teixeluis/clustered-heating-controller/docs/adapter_board/io_adapter_board.kicad_sch

## KiCad design docs/adapter_board/io_adapter_board.kicad_sch (2024-08-31)

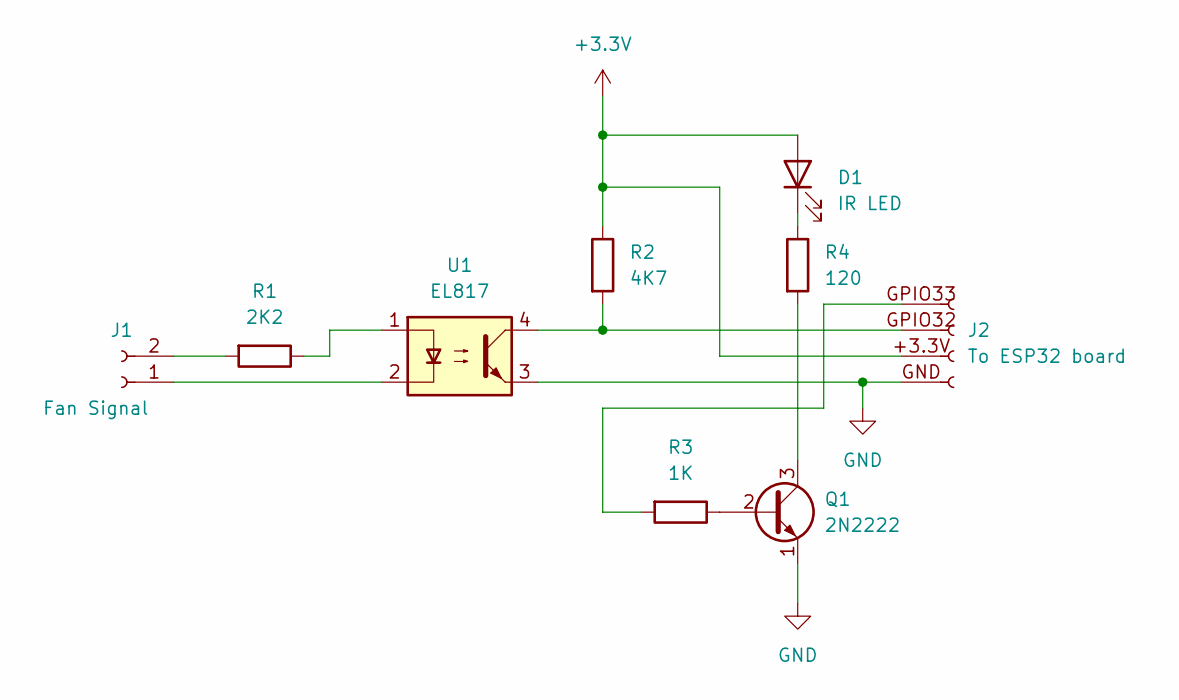
[picture p19: schematic io_adapter_board.kicad_sch]

Parts:
D1: IR LED
J1: Fan Signal
J2: To ESP32 board
Q1: 2N2222; TO-39-3
R1: 2K2
R2: 4K7
R3: 1K
R4: 120
U1: EL817; DIP-4_W7.62mm

Connections:
unnamed: D1.1 (K), R4.1
unnamed: D1.2 (A), J2.+3.3V (Pin_3), R2.1
unnamed: J1.1, U1.2
unnamed: J1.2, R1.2
unnamed: J2.GND (Pin_4), U1.3
unnamed: J2.GPIO32 (Pin_2), R2.2, U1.4
unnamed: J2.GPIO33 (Pin_1), R3.2
unnamed: Q1.2 (B), R3.1
unnamed: Q1.3 (C), R4.2
unnamed: R1.1, U1.1
