teixeluis/clustered-heating-controller/docs/current_sensor/current_sensor.kicad_sch

## KiCad design docs/current_sensor/current_sensor.kicad_sch (2024-08-26)

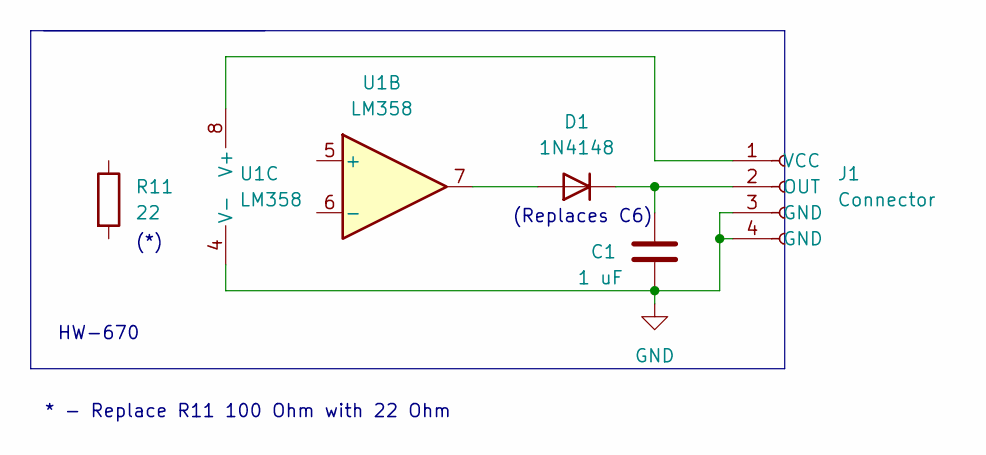
[picture p20: schematic current_sensor.kicad_sch]

Parts:
C1: 1 uF
D1: 1N4148; D_DO-35_SOD27_P7.62mm_Horizontal
J1: Connector
R11: 22
U1: LM358

Connections:
unnamed: C1.1, D1.1 (K), J1.2 (OUT)
unnamed: C1.2, J1.3 (GND), J1.4 (GND), U1.4 (V-)
unnamed: D1.2 (A), U1.7
unnamed: J1.1 (VCC), U1.8 (V+)

Notes on the sheet:
(Replaces C6)
HW-670
(*)
* - Replace R11 100 Ohm with 22 Ohm
