teixeluis/clustered-heating-controller/docs/heater_mod/heater_modification.kicad_sch

## KiCad design docs/heater_mod/heater_modification.kicad_sch (2024-08-26)

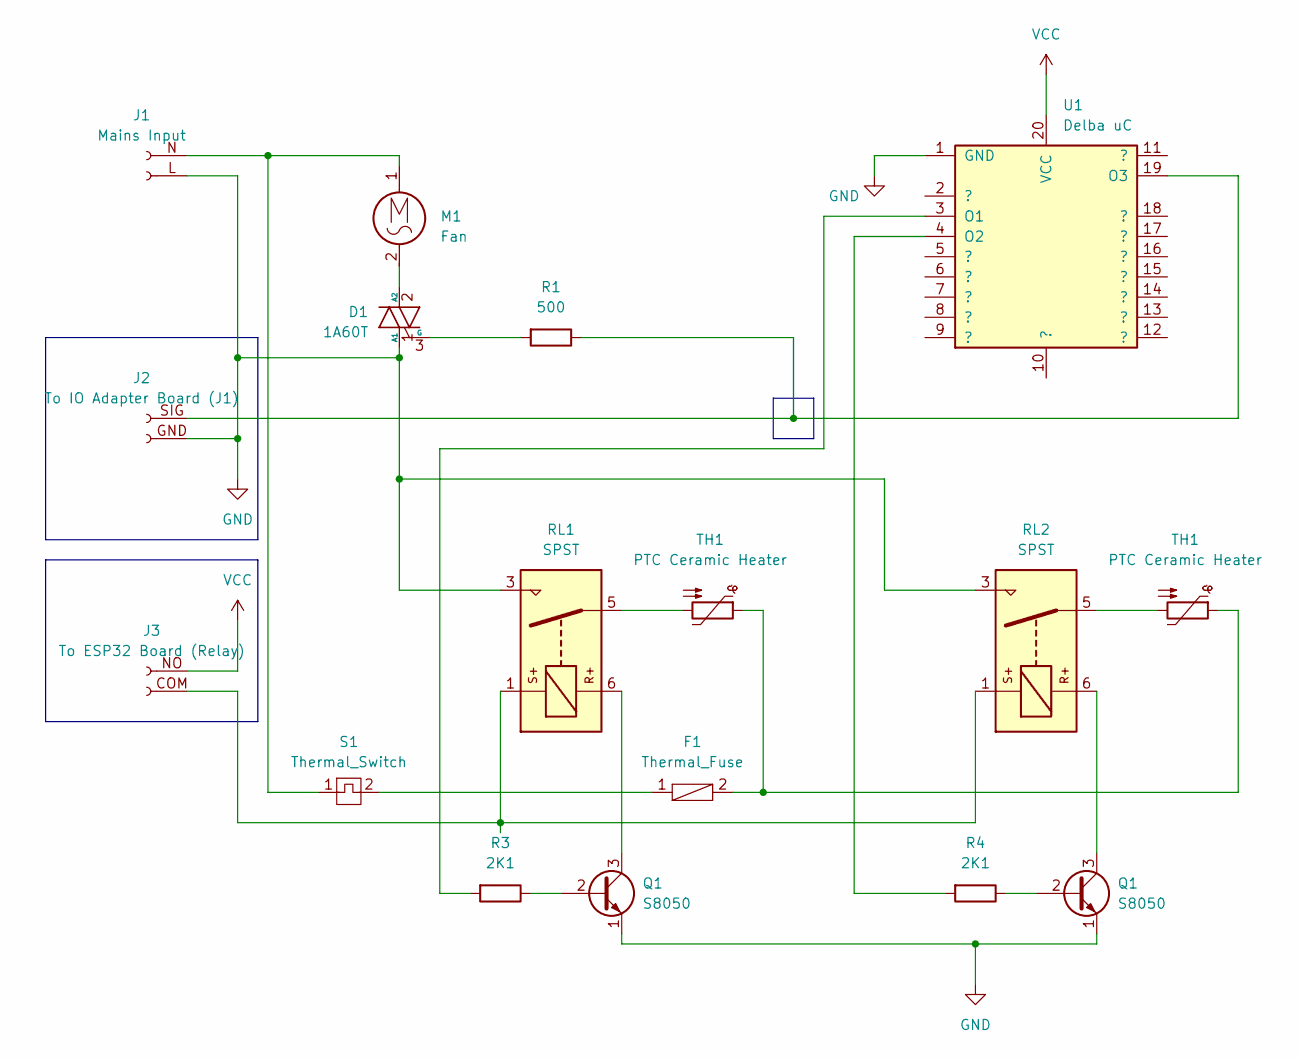
[picture p21: schematic heater_modification.kicad_sch]

Parts:
D1: 1A60T
F1: Thermal_Fuse
J1: Mains Input
J2: To IO Adapter Board (J1)
J3: To ESP32 Board (Relay)
M1: Fan
Q1: S8050; TO-92_Inline
R1: 500
R3, R4: 2K1
RL1, RL2: SPST; Relay_1P1T_NO_10x24x18.8mm_Panasonic_ADW11xxxxW_THT
S1: Thermal_Switch
TH1: PTC Ceramic Heater
U1: Delba uC

Connections:
unnamed: D1.1 (A1), J1.L (Live), J2.GND (Pin_2), RL1.3, RL2.3
unnamed: D1.2 (A2), M1.2
unnamed: D1.3 (G), R1.2
unnamed: F1.1, S1.2
unnamed: F1.2, TH1.1
unnamed: J1.N (L), M1.1, S1.1
unnamed: J2.SIG (Pin_1), R1.1, U1.19 (O3)
unnamed: J3.COM (Pin_2), RL1.1, RL2.1
unnamed: Q1.2 (B), R3.1, R4.1
unnamed: Q1.3 (C), RL1.6, RL2.6
unnamed: R3.2, U1.3 (O1)
unnamed: R4.2, U1.4 (O2)
unnamed: RL1.5, TH1.2
unnamed: RL2.5, TH1.2
